swharden/QRSS-hardware/graphics/diagrams/amplifier-2n7000-sound.whsites.net.gif

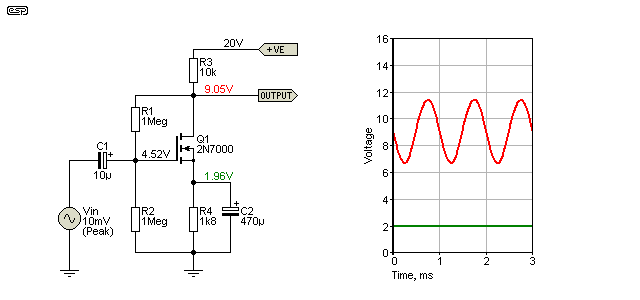
graphics/diagrams/amplifier-2n7000-sound.whsites.net.gif
