swharden/QRSS-hardware/graphics/diagrams/amplifier-IRF510-kd7rem.gif

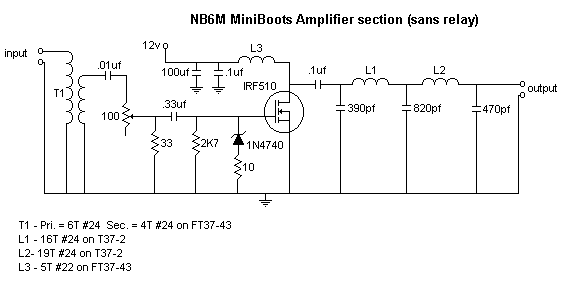
graphics/diagrams/amplifier-IRF510-kd7rem.gif
