swharden/QRSS-hardware/graphics/diagrams/amplifier-IRF510-va3iul.jpg

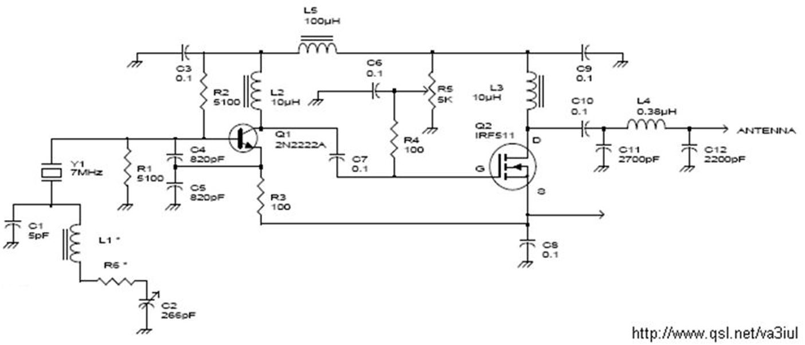
graphics/diagrams/amplifier-IRF510-va3iul.jpg
