swharden/QRSS-hardware/spots/2019-07-21/W4HBK1.1907210820.7bfd9fbd3b.jpg

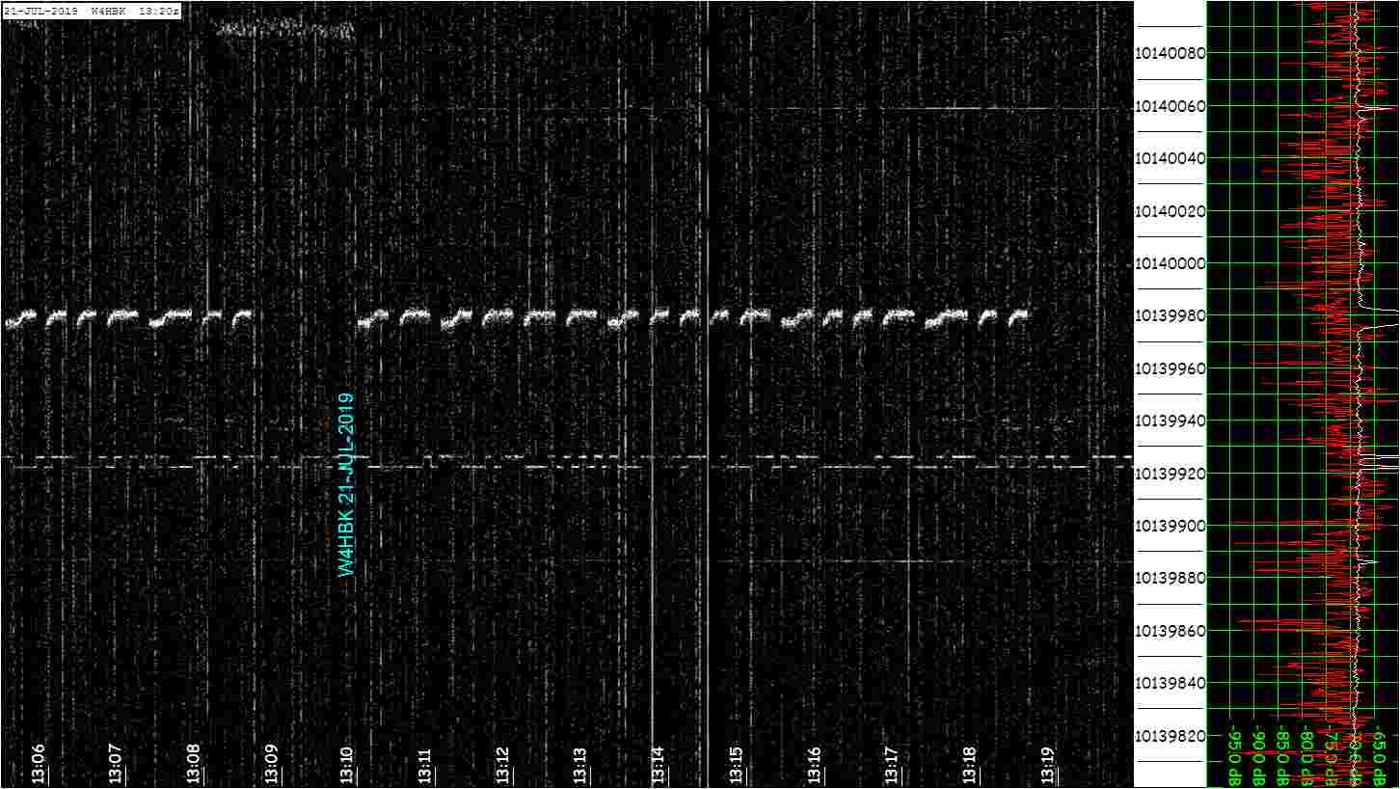
spots/2019-07-21/W4HBK1.1907210820.7bfd9fbd3b.jpg
