swharden/QRSS-hardware/spots/2019-07-21/W4HBK1.1907212320.18d62e961e.jpg

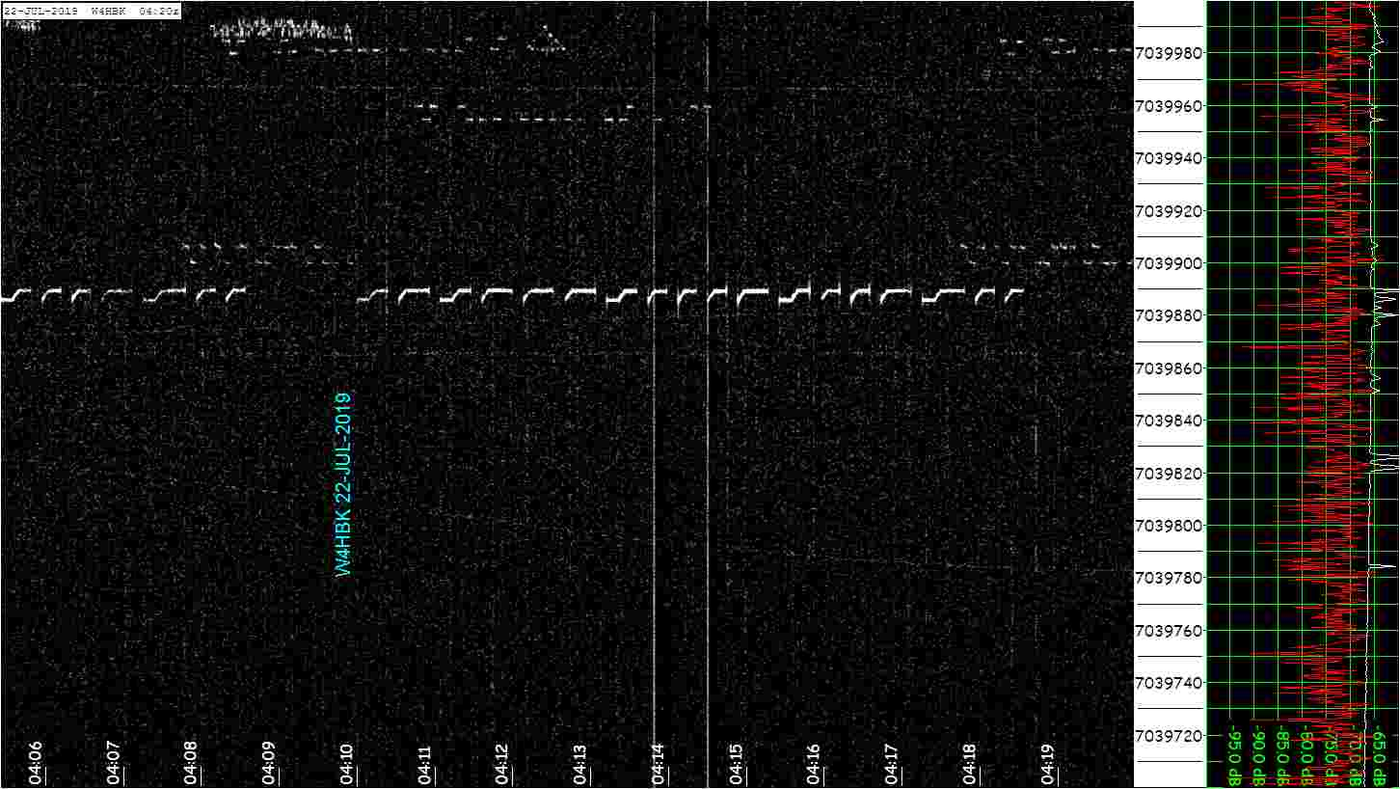
spots/2019-07-21/W4HBK1.1907212320.18d62e961e.jpg
