swharden/QRSS-hardware/spots/2019-07-21/WD4AH.1907210800.6729108296.jpg

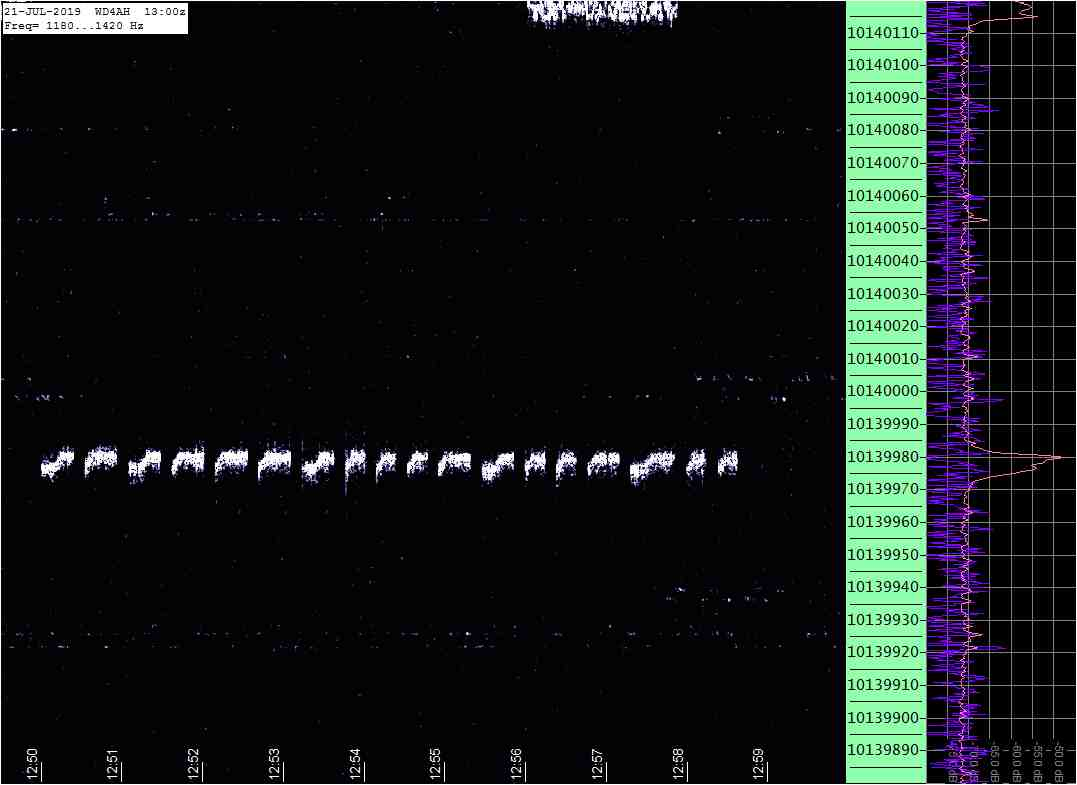
spots/2019-07-21/WD4AH.1907210800.6729108296.jpg
