swharden/QRSS-hardware/spots/2019-07-24/WA5DJJ-30m.1907242120-stack13.jpg

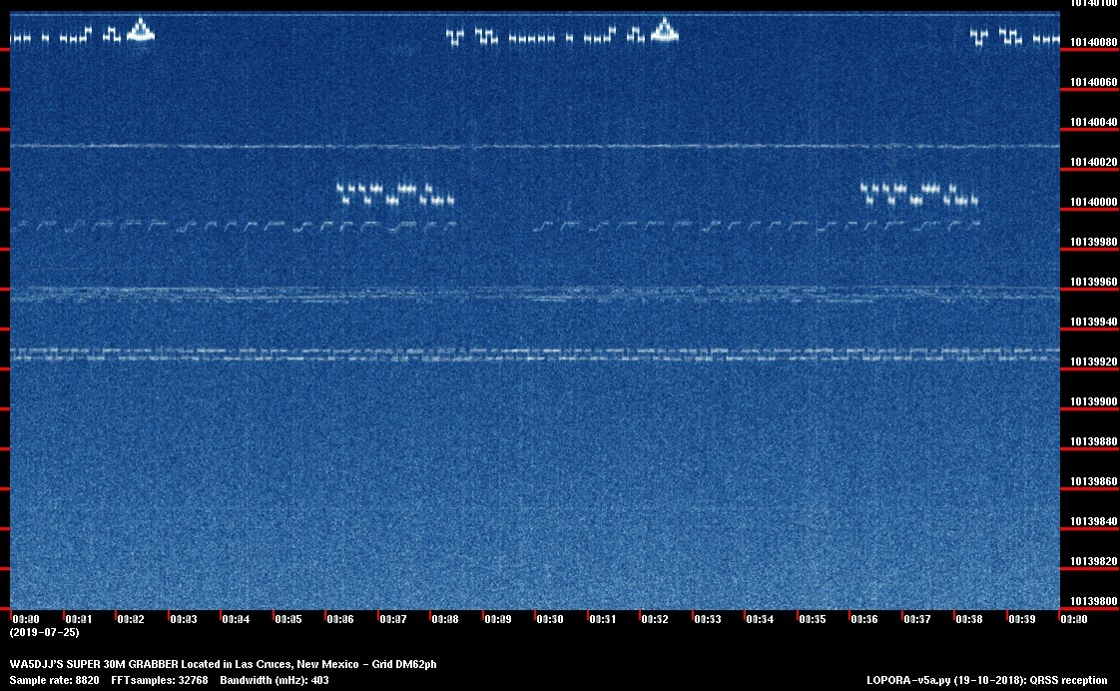
spots/2019-07-24/WA5DJJ-30m.1907242120-stack13.jpg
