swharden/QRSS-hardware/builds/amplifier/LTspice/Draft3.jpg

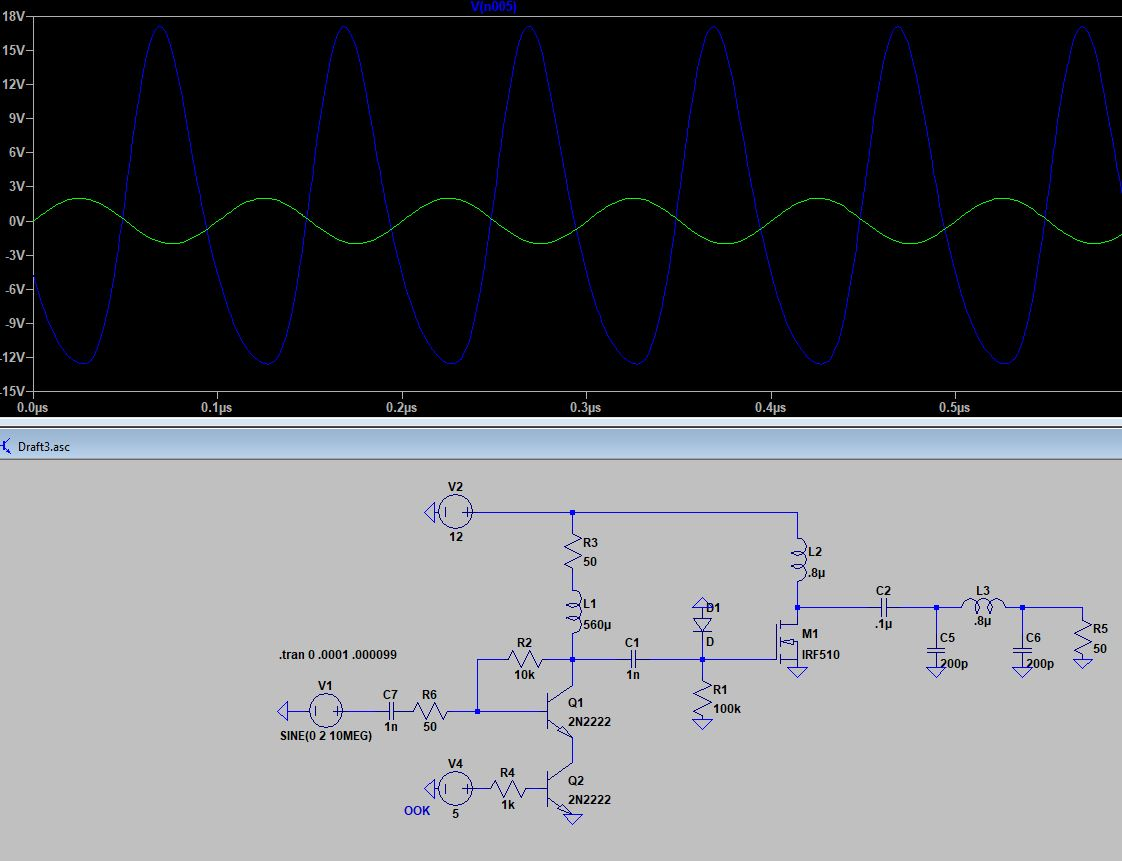
builds/amplifier/LTspice/Draft3.jpg
