swharden/QRSS-hardware/graphics/builds/2019-07-19-oven.jpg

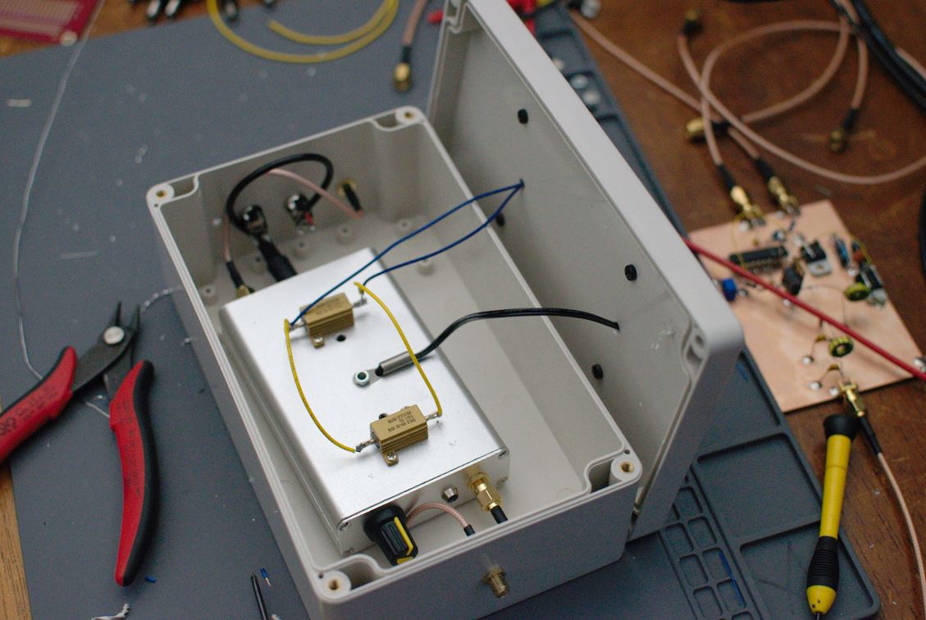
graphics/builds/2019-07-19-oven.jpg
