swharden/QRSS-hardware/builds/amplifier/LTspice/Draft1.asc

C1: cap; .1µ
C2: cap; 1µ
D1: diode; 1N4148
L1: ind; 0.8µH
M1: nmos; IRF510
Q1: npn; 2N3904
R1: res; 100k
R2: res; 100k
R3: res; 10k
R5: res; 50
V1: voltage; SINE(2.5 2 10MEG)
V2: voltage; 12
V3: voltage; 0
Named nets: 0
.tran 0 .0001 .000099
