swharden/QRSS-hardware/builds/amplifier/LTspice/Draft2.asc

C1: cap; 1n
C2: cap; .1µ
C3: cap; 1n
C5: cap; 200p
C6: cap; 200p
C7: cap; 1n
D1: diode; 1N4148
D2: diode; 1N4148
L1: ind; .8µ
L2: ind; .8µ
L3: ind; .8µ
M1: nmos; IRF510
M2: nmos; 2N7002
R1: res; 100k
R3: res; 100k
R4: res; 50
R5: res; 50
V1: voltage; SINE(0 2 10MEG)
V2: voltage; 12
V4: voltage; 2
Named nets: 0
.tran 0 .0001 .000099
