swharden/QRSS-hardware/builds/amplifier/LTspice/Draft3.asc

C1: cap; 1n
C2: cap; .1µ
C5: cap; 200p
C6: cap; 200p
C7: cap; 1n
D1: diode
L1: ind; 560µ
L2: ind; .8µ
L3: ind; .8µ
M1: nmos; IRF510
Q1: npn; 2N2222
Q2: npn; 2N2222
R1: res; 100k
R2: res; 10k
R3: res; 50
R4: res; 1k
R5: res; 50
R6: res; 50
V1: voltage; SINE(0 2.25 10MEG)
V2: voltage; 12
V4: voltage; 5
Named nets: 0
.tran 0 .0001 .000099
OOK
