swharden/QRSS-hardware/builds/keyer/fsk-circuit/fsk-circuit.sch

## KiCad design builds/keyer/fsk-circuit/fsk-circuit.sch (2019-07-21)

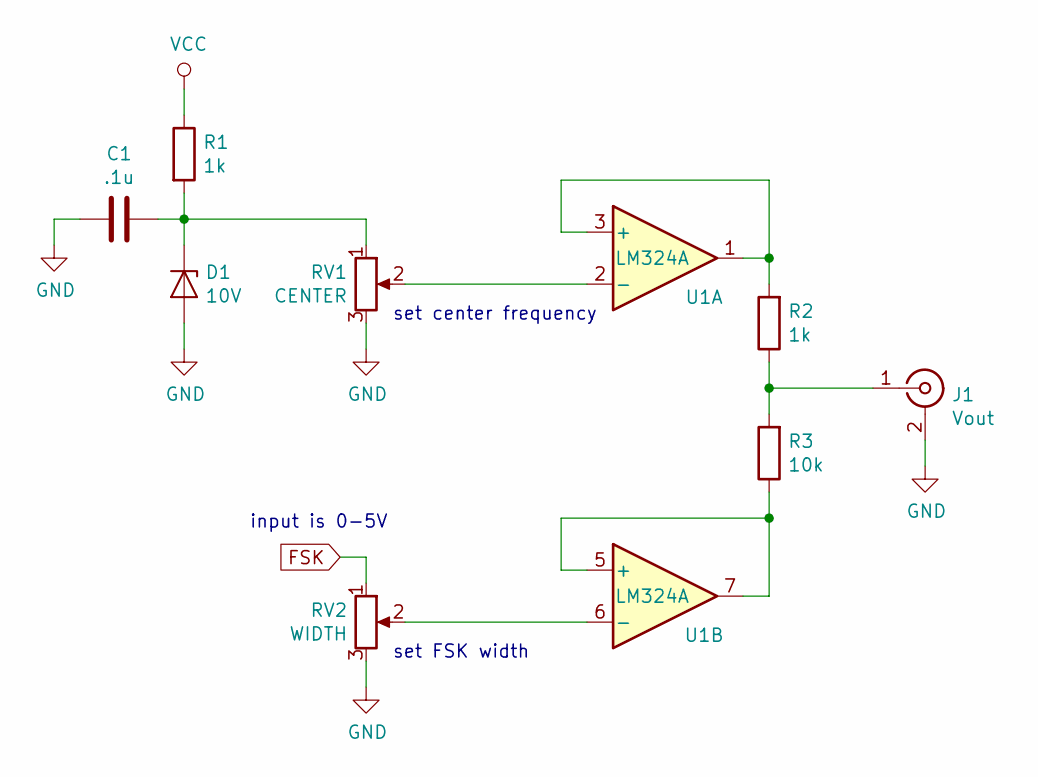
[picture p107: schematic fsk-circuit.sch]

Parts:
C1: .1u
D1: 10V
J1: Vout
R1, R2: 1k
R3: 10k
RV1: CENTER
RV2: WIDTH
U1: LM324A

Connections:
FSK: RV2.1
GND: C1.2, D1.2 (A), J1.2 (Ext), RV1.3, RV2.3
unnamed: C1.1, D1.1 (K), R1.2, RV1.1
unnamed: J1.1 (In), R2.1, R3.2
unnamed: R2.2, U1.1, U1.3 (+)
unnamed: R3.1, U1.5 (+), U1.7
unnamed: RV1.2, U1.2 (-)
unnamed: RV2.2, U1.6 (-)
VCC: R1.1

Notes on the sheet:
set center frequency
set FSK width
input is 0-5V
