swharden/QRSS-hardware/builds/oven/2019-07-14 lazy oven/kicad/oven.sch

## KiCad design builds/oven/2019-07-14 lazy oven/kicad/oven.sch (2019-07-14)

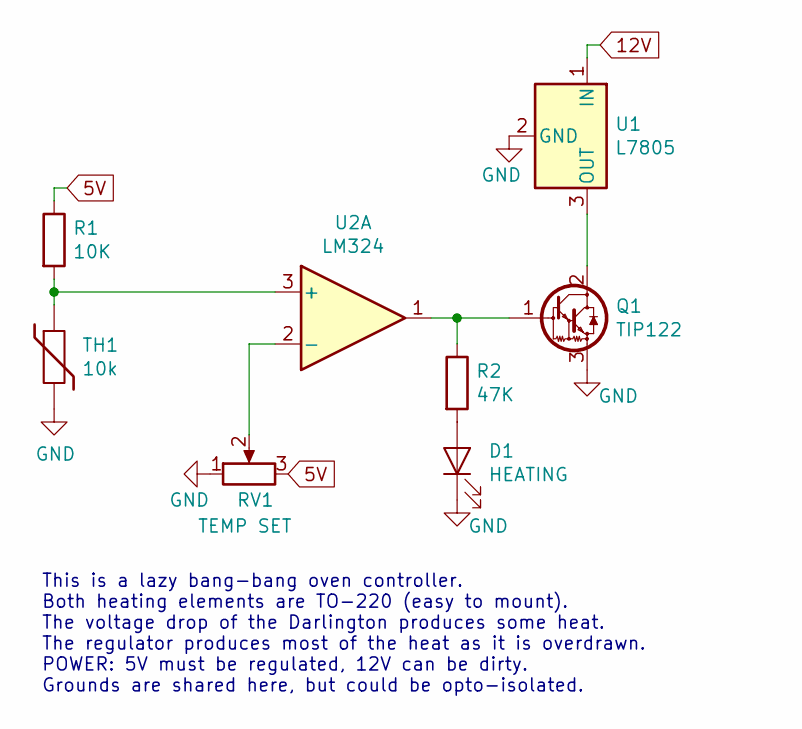
[picture p108: schematic oven.sch]

Parts:
D1: HEATING
Q1: TIP122; TO-220-3_Vertical
R1: 10K
R2: 47K
RV1: TEMP SET
TH1: 10k
U1: L7805
U2: LM324

Connections:
5V: R1.1, RV1.3
12V: U1.1 (IN)
GND: D1.1 (K), Q1.3 (E), RV1.1, TH1.2, U1.2 (GND)
unnamed: D1.2 (A), R2.2
unnamed: Q1.1 (B), R2.1, U2.1
unnamed: Q1.2 (C), U1.3 (OUT)
unnamed: R1.2, TH1.1, U2.3 (+)
unnamed: RV1.2, U2.2 (-)

Notes on the sheet:
This is a lazy bang-bang oven controller. Both heating elements are TO-220 (easy to mount). The voltage drop of the Darlington produces some heat. The regulator produces most of the heat as it is overdrawn. POWER: 5V must be regulated, 12V can be dirty. Grounds are shared here, but could be opto-is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
