swharden/QRSS-hardware/builds/oven/2019-07-15 chassis heater/kicad/oven.sch

## KiCad design builds/oven/2019-07-15 chassis heater/kicad/oven.sch (2019-07-15)

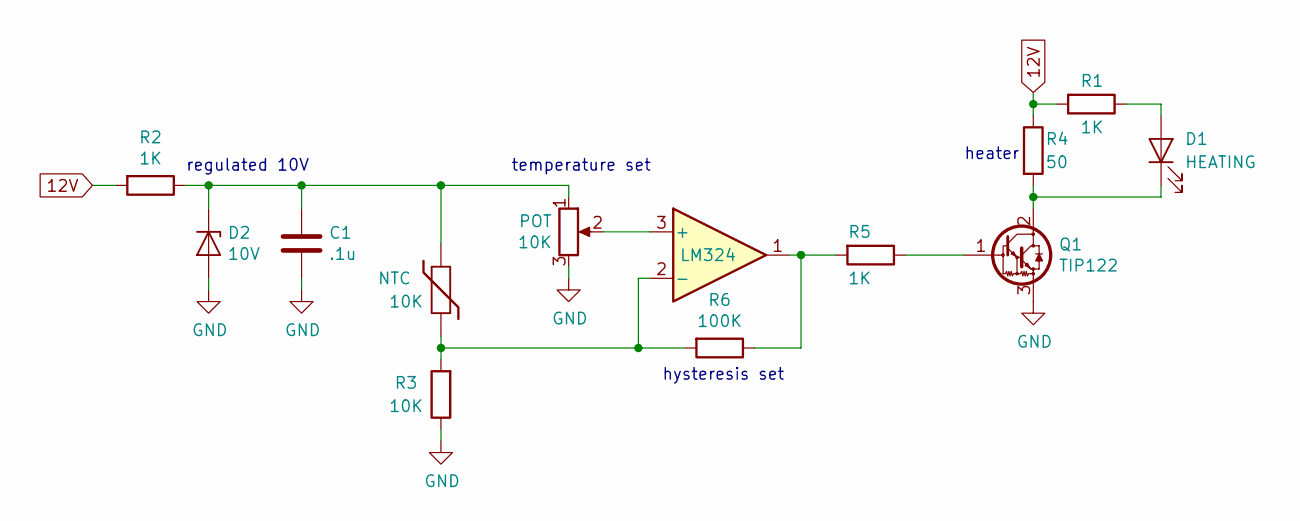
[picture p110: schematic oven.sch]

Parts:
C1: .1u
D1: HEATING
D2: 10V
NTC: 10K
POT: 10K
Q1: TIP122; TO-220-3_Vertical
R1, R2, R5: 1K
R3: 10K
R4: 50
R6: 100K
U1: LM324

Connections:
12V: R1.2, R2.2, R4.1
GND: C1.2, D2.2 (A), POT.3, Q1.3 (E), R3.1
unnamed: C1.1, D2.1 (K), NTC.2, POT.1, R2.1
unnamed: D1.1 (K), Q1.2 (C), R4.2
unnamed: D1.2 (A), R1.1
unnamed: NTC.1, R3.2, R6.2, U1.2 (-)
unnamed: POT.2, U1.3 (+)
unnamed: Q1.1 (B), R5.1
unnamed: R5.2, R6.1, U1.1

Notes on the sheet:
hysteresis set
heater
regulated 10V
temperature set
